Gaboze-Pocaio/Gaboze-Pocaio-Round-2---Perfect/images/001.jpg

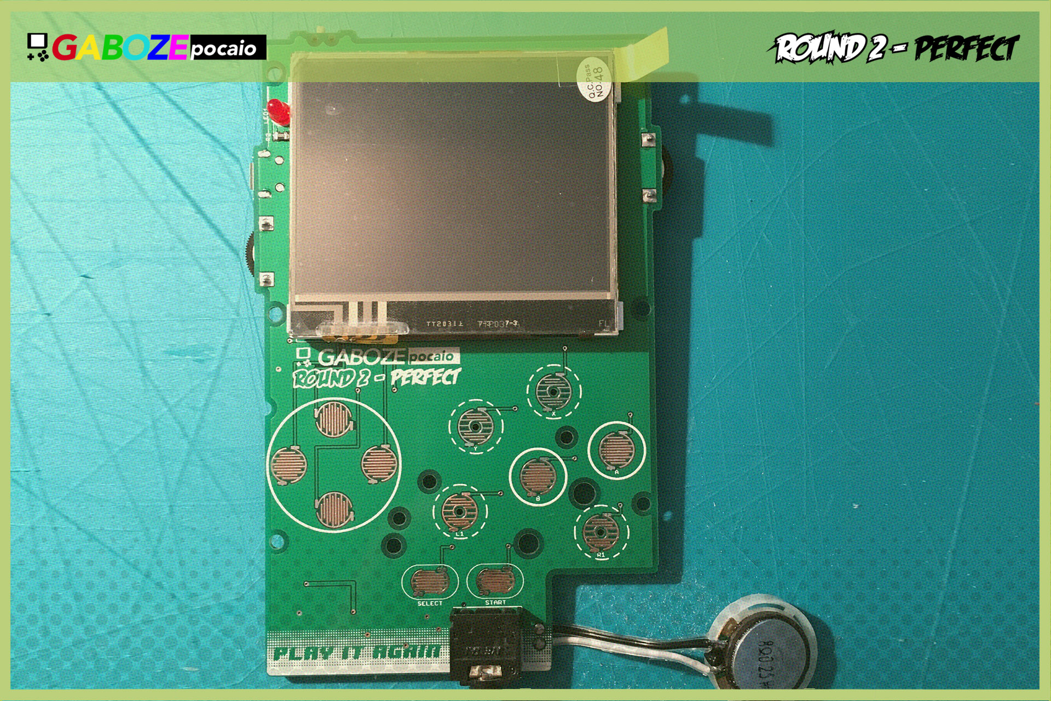
images/001.jpg
